JakobThiessen/RoboticLawnMower/Embedded/Mainboard/Mainboard/taskEnvSensor.h

/*
 * taskEnvSensor.h
 *
 * Created: 24.03.2023 18:57:01
 *  Author: jakob
 */ 


#ifndef TASK_ENV_SENSOR_H_
#define TASK_ENV_SENSOR_H_

void vEnvSensorTask(void* pvParameters);



#endif /* TASKENVSENSOR_H_ */
