JakobThiessen/RoboticLawnMower/Embedded/Mainboard/Mainboard/driver/VL53L1X/API/platform/vl53l1_platform.c

/* 
* This file is part of VL53L1 Platform 
* 
* Copyright (c) 2016, STMicroelectronics - All Rights Reserved 
* 
* License terms: BSD 3-clause "New" or "Revised" License. 
* 
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
* 3. Neither the name of the copyright holder nor the names of its contributors 
* may be used to endorse or promote products derived from this software 
* without specific prior written permission. 
* 
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
*/

#include "vl53l1_platform.h"
#include <string.h>
#include <time.h>
#include <math.h>

#define I2C_TIME_OUT_BASE   10
#define I2C_TIME_OUT_BYTE   1

static struct vl53l1_dev intf;

int8_t VL53L1_initInterface(uint8_t chip_id, vl53l1_iic_Read_t read, vl53l1_iic_Write_t write)
{
	intf.chip_id = chip_id;
	intf.read = read;
	intf.write = write;
	
	/* Those basic I2C read functions can be used to check your own I2C functions */
	uint8_t byteData = 0;
	uint8_t sensorState = 0;
	uint16_t wordData = 0;
	
	int status = VL53L1_RdByte(chip_id, 0x010F, &byteData);
//	printf("VL53L1X Model_ID: %X\n", byteData);
	status = VL53L1_RdByte(chip_id, 0x0110, &byteData);
//	printf("VL53L1X Module_Type: %X\n", byteData);
	status = VL53L1_RdWord(chip_id, 0x010F, &wordData);
//	printf("VL53L1X: %X\n", wordData);
	while(sensorState==0)
	{
		status = VL53L1X_BootState(chip_id, &sensorState);
		//HAL_Delay(2);
	}
//	printf("Chip booted\n");
	
	return 0;
}

uint8_t _I2CBuffer[256];

int _I2CWrite(uint16_t Dev, uint8_t *pdata, uint32_t count)
{
	int status;
	int i2c_time_out = I2C_TIME_OUT_BASE+ count* I2C_TIME_OUT_BYTE;

	//status = HAL_I2C_Master_Transmit(&XNUCLEO53L1A1_hi2c, Dev, pdata, count, i2c_time_out);
	intf.write(intf.chip_id, pdata, count);

	return status = 0;
}

int _I2CRead(uint16_t Dev, uint8_t *pdata, uint32_t count)
{
	int status = 0;
	int i2c_time_out = I2C_TIME_OUT_BASE+ count* I2C_TIME_OUT_BYTE;

	//status = HAL_I2C_Master_Receive(&XNUCLEO53L1A1_hi2c, Dev|1, pdata, count, i2c_time_out);
	intf.read(intf.chip_id, pdata, count);
	
	return status;
}

VL53L1_Error VL53L1_WriteMulti(uint16_t Dev, uint16_t index, uint8_t *pdata, uint32_t count)
{
    int status_int;
    VL53L1_Error Status = VL53L1_ERROR_NONE;
    if (count > sizeof(_I2CBuffer) - 1)
	{
        return VL53L1_ERROR_INVALID_PARAMS;
    }
    _I2CBuffer[0] = index>>8;
    _I2CBuffer[1] = index&0xFF;
    memcpy(&_I2CBuffer[2], pdata, count);

    status_int = _I2CWrite(Dev, _I2CBuffer, count + 2);
    if (status_int != 0) {
        Status = VL53L1_ERROR_CONTROL_INTERFACE;
    }

    return Status;
}

// the ranging_sensor_comms.dll will take care of the page selection
VL53L1_Error VL53L1_ReadMulti(uint16_t Dev, uint16_t index, uint8_t *pdata, uint32_t count)
{
    VL53L1_Error Status = VL53L1_ERROR_NONE;
    int32_t status_int;

    _I2CBuffer[0] = index>>8;
    _I2CBuffer[1] = index&0xFF;

    status_int = _I2CWrite(Dev, _I2CBuffer, 2);
    if (status_int != 0) {
        Status = VL53L1_ERROR_CONTROL_INTERFACE;
    }
    status_int = _I2CRead(Dev, pdata, count);
    if (status_int != 0) {
        Status = VL53L1_ERROR_CONTROL_INTERFACE;
    }
    return Status;
}

VL53L1_Error VL53L1_WrByte(uint16_t Dev, uint16_t index, uint8_t data)
{
    VL53L1_Error Status = VL53L1_ERROR_NONE;
    int32_t status_int;

    _I2CBuffer[0] = index>>8;
    _I2CBuffer[1] = index&0xFF;
    _I2CBuffer[2] = data;


    status_int = _I2CWrite(Dev, _I2CBuffer, 3);
    if (status_int != 0) {
        Status = VL53L1_ERROR_CONTROL_INTERFACE;
    }

    return Status;
}

VL53L1_Error VL53L1_WrWord(uint16_t Dev, uint16_t index, uint16_t data)
{
    VL53L1_Error Status = VL53L1_ERROR_NONE;
    int32_t status_int;

    _I2CBuffer[0] = index>>8;
    _I2CBuffer[1] = index&0xFF;
    _I2CBuffer[2] = data >> 8;
    _I2CBuffer[3] = data & 0x00FF;


    status_int = _I2CWrite(Dev, _I2CBuffer, 4);
    if (status_int != 0) {
        Status = VL53L1_ERROR_CONTROL_INTERFACE;
    }

    return Status;
}

VL53L1_Error VL53L1_WrDWord(uint16_t Dev, uint16_t index, uint32_t data)
{
    VL53L1_Error Status = VL53L1_ERROR_NONE;
    int32_t status_int;
    _I2CBuffer[0] = index>>8;
    _I2CBuffer[1] = index&0xFF;
    _I2CBuffer[2] = (data >> 24) & 0xFF;
    _I2CBuffer[3] = (data >> 16) & 0xFF;
    _I2CBuffer[4] = (data >> 8)  & 0xFF;
    _I2CBuffer[5] = (data >> 0 ) & 0xFF;

    status_int = _I2CWrite(Dev, _I2CBuffer, 6);
    if (status_int != 0) {
        Status = VL53L1_ERROR_CONTROL_INTERFACE;
    }

    return Status;
}

VL53L1_Error VL53L1_UpdateByte(uint16_t Dev, uint16_t index, uint8_t AndData, uint8_t OrData)
{
    VL53L1_Error Status = VL53L1_ERROR_NONE;
    uint8_t data;

    Status = VL53L1_RdByte(Dev, index, &data);
    if (Status) {
        goto done;
    }
    data = (data & AndData) | OrData;
    Status = VL53L1_WrByte(Dev, index, data);
done:
    return Status;
}

VL53L1_Error VL53L1_RdByte(uint16_t Dev, uint16_t index, uint8_t *data)
{
    VL53L1_Error Status = VL53L1_ERROR_NONE;
    int32_t status_int;

	_I2CBuffer[0] = index>>8;
	_I2CBuffer[1] = index&0xFF;

    status_int = _I2CWrite(Dev, _I2CBuffer, 2);
    if( status_int ){
        Status = VL53L1_ERROR_CONTROL_INTERFACE;
        goto done;
    }
    status_int = _I2CRead(Dev, data, 1);
    if (status_int != 0) {
        Status = VL53L1_ERROR_CONTROL_INTERFACE;
    }
done:

    return Status;
}

VL53L1_Error VL53L1_RdWord(uint16_t Dev, uint16_t index, uint16_t *data)
{
    VL53L1_Error Status = VL53L1_ERROR_NONE;
    int32_t status_int;

    _I2CBuffer[0] = index>>8;
	_I2CBuffer[1] = index&0xFF;

    status_int = _I2CWrite(Dev, _I2CBuffer, 2);

    if( status_int ){
        Status = VL53L1_ERROR_CONTROL_INTERFACE;
        goto done;
    }
    status_int = _I2CRead(Dev, _I2CBuffer, 2);
    if (status_int != 0) {
        Status = VL53L1_ERROR_CONTROL_INTERFACE;
        goto done;
    }

    *data = ((uint16_t)_I2CBuffer[0]<<8) + (uint16_t)_I2CBuffer[1];
done:

    return Status;
}

VL53L1_Error VL53L1_RdDWord(uint16_t Dev, uint16_t index, uint32_t *data)
{
    VL53L1_Error Status = VL53L1_ERROR_NONE;
    int32_t status_int;

    _I2CBuffer[0] = index>>8;
	_I2CBuffer[1] = index&0xFF;

    status_int = _I2CWrite(Dev, _I2CBuffer, 2);
    if (status_int != 0) {
        Status = VL53L1_ERROR_CONTROL_INTERFACE;
        goto done;
    }
    status_int = _I2CRead(Dev, _I2CBuffer, 4);
    if (status_int != 0) {
        Status = VL53L1_ERROR_CONTROL_INTERFACE;
        goto done;
    }

    *data = ((uint32_t)_I2CBuffer[0]<<24) + ((uint32_t)_I2CBuffer[1]<<16) + ((uint32_t)_I2CBuffer[2]<<8) + (uint32_t)_I2CBuffer[3];

done:

    return Status;
}

VL53L1_Error VL53L1_GetTickCount(uint32_t *ptick_count_ms)
{

    /* Returns current tick count in [ms] */

	VL53L1_Error status  = VL53L1_ERROR_NONE;

	//*ptick_count_ms = timeGetTime();
	*ptick_count_ms = 0;
	
	return status;
}
