JakobThiessen/RoboticLawnMower/Embedded/Mainboard/Mainboard/taskCommuncation.h

/*
 * taskEnvSensor.h
 *
 * Created: 24.03.2023 18:57:01
 *  Author: jakob
 */ 


#ifndef TASK_COMMUNCATION_H_
#define TASK_COMMUNCATION_H_

void vCommunicationTask(void* pvParameters);



#endif /* TASKENVSENSOR_H_ */
