JakobThiessen/RoboticLawnMower/Embedded/Mainboard/Mainboard/driver/opt3001/opt3001demo.c

/*
#include <OPT3001.h>

#define OPT3001_ADDRESS 0x45

void main()
{
	opt3001_init(OPT3001_ADDRESS);
	opt3001.readManufacturerID();

	opt3001.readDeviceID();
	configureSensor();
	printResult("High-Limit", opt3001.readHighLimit());
	printResult("Low-Limit", opt3001.readLowLimit());

	while(1)
	{
		OPT3001 result = opt3001.readResult();
		delay(500);
	}
*/



/*
void configureSensor()
{
	OPT3001_Config newConfig;
	
	newConfig.RangeNumber = B1100;	
	newConfig.ConvertionTime = B0;
	newConfig.Latch = B1;
	newConfig.ModeOfConversionOperation = B11;

	OPT3001_ErrorCode errorConfig = opt3001.writeConfig(newConfig);
	if (errorConfig != NO_ERROR)
		printError("OPT3001 configuration", errorConfig);
	else {
		OPT3001_Config sensorConfig = opt3001.readConfig();
		Serial.println("OPT3001 Current Config:");
		Serial.println("------------------------------");
		
		Serial.print("Conversion ready (R):");
		Serial.println(sensorConfig.ConversionReady,HEX);

		Serial.print("Conversion time (R/W):");
		Serial.println(sensorConfig.ConvertionTime, HEX);

		Serial.print("Fault count field (R/W):");
		Serial.println(sensorConfig.FaultCount, HEX);

		Serial.print("Flag high field (R-only):");
		Serial.println(sensorConfig.FlagHigh, HEX);

		Serial.print("Flag low field (R-only):");
		Serial.println(sensorConfig.FlagLow, HEX);

		Serial.print("Latch field (R/W):");
		Serial.println(sensorConfig.Latch, HEX);

		Serial.print("Mask exponent field (R/W):");
		Serial.println(sensorConfig.MaskExponent, HEX);

		Serial.print("Mode of conversion operation (R/W):");
		Serial.println(sensorConfig.ModeOfConversionOperation, HEX);

		Serial.print("Polarity field (R/W):");
		Serial.println(sensorConfig.Polarity, HEX);

		Serial.print("Overflow flag (R-only):");
		Serial.println(sensorConfig.OverflowFlag, HEX);

		Serial.print("Range number (R/W):");
		Serial.println(sensorConfig.RangeNumber, HEX);

		Serial.println("------------------------------");
	}
}
*/
